mesutpiskin/little-explorer-activity-box/artwork/activity-box-label-preview.png

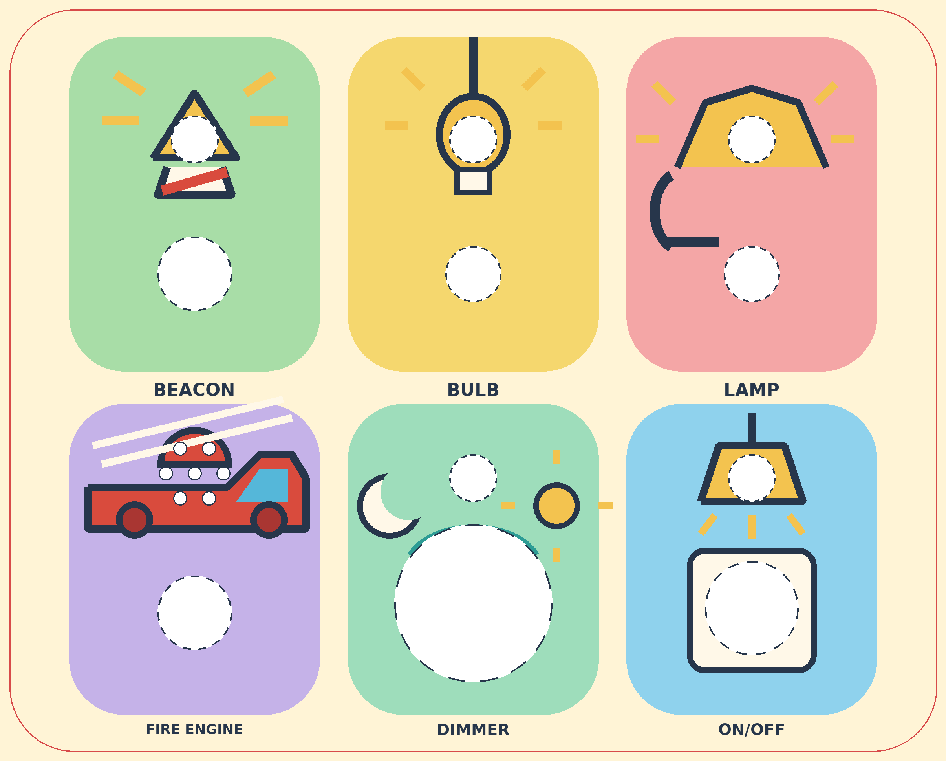
artwork/activity-box-label-preview.png
