mesutpiskin/little-explorer-activity-box/artwork/activity-box-assembled-preview.png

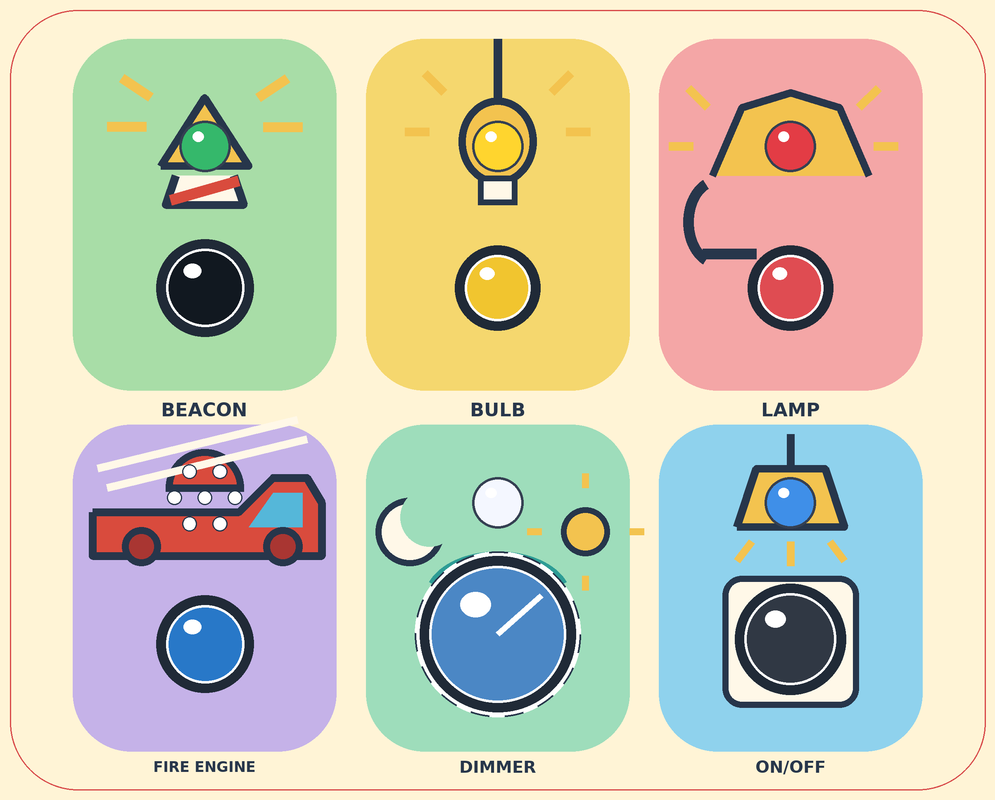
artwork/activity-box-assembled-preview.png
